joeiddon/chess_robot/model/stls/link7.stl

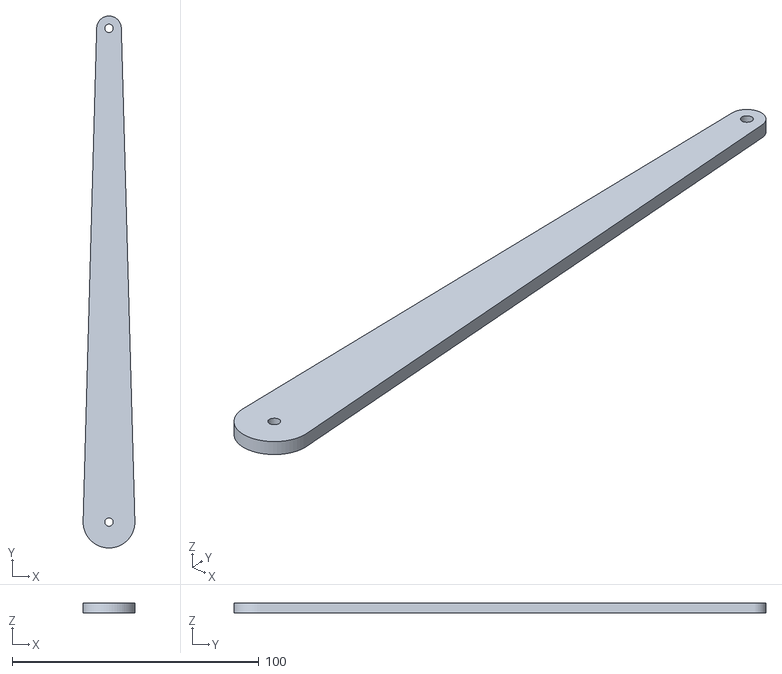
[picture p16: CAD file, 2018-08-20]
model/stls/link7.stl
21.0 x 215.5 x 3.90
