joeiddon/chess_robot/model/stls/link2.stl

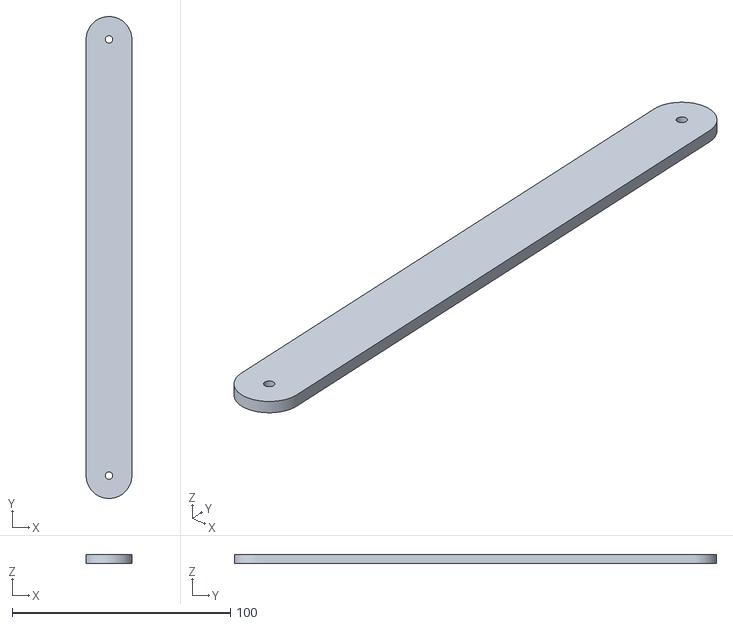
[picture p17: CAD file, 2018-08-20]
model/stls/link2.stl
21.0 x 221.0 x 3.90
