joeiddon/chess_robot/model/stls/link4.stl

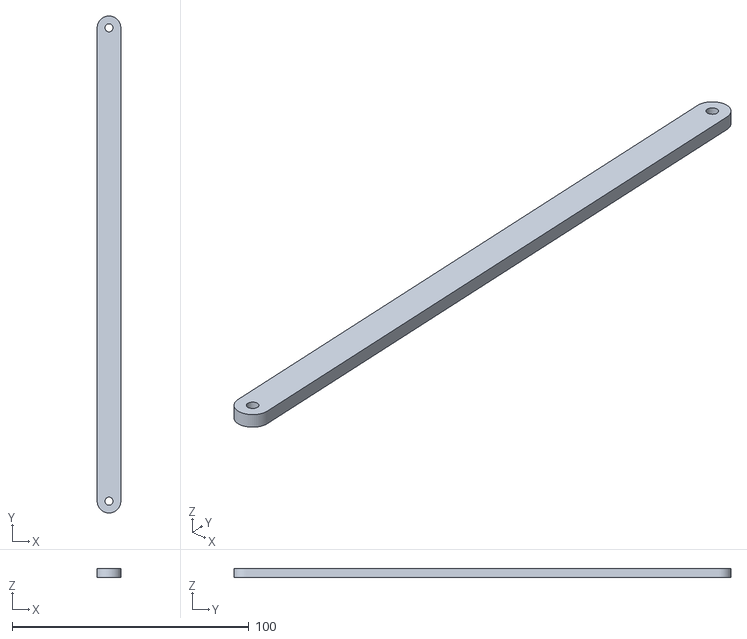
[picture p18: CAD file, 2018-08-20]
model/stls/link4.stl
10.0 x 210.0 x 3.90
