joeiddon/chess_robot/model/stls/link6.stl

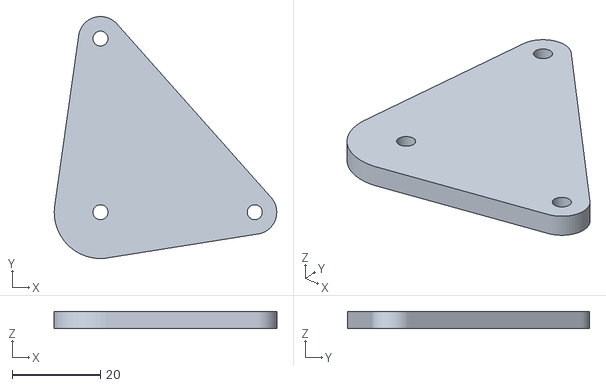
[picture p19: CAD file, 2018-08-20]
model/stls/link6.stl
50.5 x 54.9 x 3.90
