joeiddon/chess_robot/model/stls/link3.stl

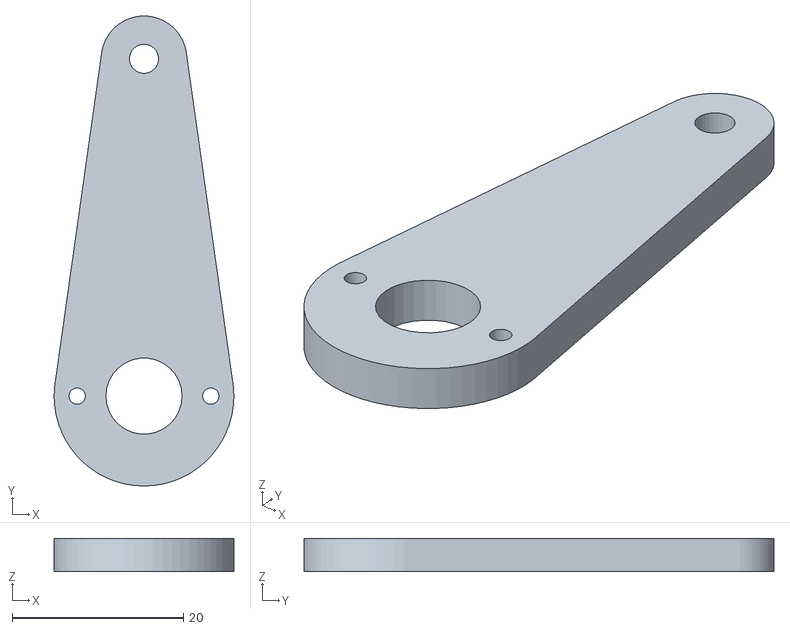
[picture p20: CAD file, 2018-08-20]
model/stls/link3.stl
21.0 x 54.9 x 3.90
