joeiddon/chess_robot/model/scads/link4.scad

//general
$fn = 30;                  //convexity of general curved faces
thickness = 3.9;             //thickness of arm

//arm specific stuff
arm_length =  200;//155;               //horn center to horn center distance for arm length

pivot_diameter = 10;            //diameter of pivoting end
free_turning3mm = 3.4;          //diameter of hole for free turning motion

difference(){
   hull(){
      cylinder(d=pivot_diameter,h=thickness, $fn = 60);
      translate([0,arm_length,0])
      cylinder(d=pivot_diameter,h=thickness, $fn = 60);
   }
   cylinder(d=free_turning3mm,h=thickness);
   translate([0,arm_length,0])
   cylinder(d=free_turning3mm,h=thickness);
}
