joeiddon/chess_robot/recognition.py

import vision
import numpy as np

def recognise(display=False):
    """
    Operation:
     - determine where the chess board is
     - count the number of pixels in each grid square
     - if this is over a limit, say that there is a piece there
     - all the pieces which pass the black threshold are black
     - if they only pass the white threshold, they're white
     - returns a tuple of 8x8 numpy arrays for white and black pieces
    """

    #general
    line_col = 255

    #detection thresholds
    white_pix_thresh = 100 #threshold for pix to count as white
    black_pix_thresh = 55  #threshold for pix to count as black
    white_pix_no = 2 #number of white threshed pixels for piece
    black_pix_no = 2 #number of black threshed pixels for piece

    #pixels of each edge of chess board
    #(hard coded because board's position must be fixed anyway for arm)
    t_edge = 12
    b_edge = 78
    l_edge = 35
    r_edge = 101

    #size of one grid square in pixels
    sqr_sz = ((r_edge-l_edge)+(b_edge-t_edge))/16

    #get the image
    raw  = vision.raw_img(128, 96)
    grey = vision.greyscale(raw)
    #blr  = vision.gaussianBlur(grey, 3, 1.5)
    #sbl  = vision.sobel(blr)

    black_threshed = grey < black_pix_thresh
    white_threshed = grey < white_pix_thresh

    black_pieces = np.zeros((8,8), 'bool')
    white_pieces = np.zeros((8,8), 'bool')

    for y in range(8):
        for x in range(8):
            l = l_edge + int( x    * sqr_sz)
            r = l_edge + int((x+1) * sqr_sz)
            t = t_edge + int( y    * sqr_sz)
            b = t_edge + int((y+1) * sqr_sz)

            black_sqr = black_threshed[t:b,l:r]
            white_sqr = white_threshed[t:b,l:r]
            is_black_piece = np.sum(black_sqr) > black_pix_no
            is_white_piece = np.sum(white_sqr) > white_pix_no

            if is_white_piece:
                if is_black_piece:
                    black_pieces[y][x] = 1
                else:
                    white_pieces[y][x] = 1

            if display:
                grey[t:b,l] = line_col
                grey[t:b,r] = line_col
                grey[t,l:r] = line_col
                grey[b,l:r] = line_col

    if display:
        import matplotlib.pyplot as plt
        grey[:,l_edge] = \
        grey[:,r_edge] = \
        grey[t_edge]   = \
        grey[b_edge]   = line_col
        print('whites:  blacks:')
        [print(w,b) for w,b in zip((''.join(str(int(i)) for i in r) for r in white_pieces),
                                   (''.join(str(int(i)) for i in r) for r in black_pieces))]
        fig = plt.gcf()
        for i,a in enumerate(('raw', 'white_threshed', 'white_pieces', 'grey', 'black_threshed', 'black_pieces')):
            ax = fig.add_subplot(2,3,i+1)
            ax.set_title(a)
            ax.imshow(locals()[a],'gray')

        plt.show()

    return (np.flip(white_pieces,1), np.flip(black_pieces,1))

if __name__ == '__main__':
    recognise(1)
